PDXostc/rvi_v2x_hardware/Simulation/ACTIVE ANTENNA.asc

C1: cap; {ccap}; V=6.3 Irms=8.6m Rser=9.56706 Lser=0 mfg="KEMET" pn="C0402C331K9RAC" type="X7R"
C2: cap; 0.1µ; V=50 Irms=835m Rser=0.0936732 Lser=0 mfg="KEMET" pn="C1812C104K5RAC" type="X7R"
C3: cap; 150p
C4: cap; 100µ; V=35 Irms=.3 Rser=.26
C5: cap; 4.7µ; V=16 Irms=11 Rser=0.00897799 Lser=0 mfg="KEMET" pn="C1210C475K4RAC" type="X7R"
C6: cap; 100µ; V=35 Irms=.3 Rser=.26
C8: cap; 4.7µ; V=16 Irms=11 Rser=0.00897799 Lser=0 mfg="KEMET" pn="C1210C475K4RAC" type="X7R"
L1: ind; 56n; Ipk=0.45 Rser=0.4 Rpar=2563 Cpar=0.17p
L2: ind; 1p
L4: ind; 120n
R1: res; 50
R2: res; 50
R3: res; 50
V1: voltage; SINE(0 1 1200meg 0); AC 2 0; Rser=50
V2: voltage; 3.3; AC 0 0; Rser=.1
V3: voltage; SINE(0 1 1200meg 0); AC 2 0; Rser=50
Named nets: 0
.ac oct 100 1meg 10000meg
.step param ccap list 47p 56p 150p 270p 390p 470p
*.step param ind list 33n 47n 120n 220n
*.param ccap 530p
