PDXostc/rvi_v2x_hardware/Simulation/Charge Pump.asc

C1: cap; 100n
C2: cap; 1µ
D1: diode; 1N4148
D2: diode; 1N4148
D3: LED; AOT-2015
D4: LED; AOT-2015
D5: LED; AOT-2015
R1: res; 22
R2: res; 470
R3: res; 470
R4: res; 470
V1: voltage; PULSE(0 {volts} 0 {slew} {slew} {ton} {per} 0)
V2: voltage; {volts}
Named nets: 0
.tran .01
.param volts 2.7
.step param freq list 20k 100k
.param per {1/freq}
.param duty 0.5
.param ton  {per*duty}
.param slew 10n
