PDXostc/rvi_v2x_hardware/Simulation/J1850.asc

D1: diode; 1N4148
D2: diode; 1N4148
M1: nmos; BSZ340N08NS3
Q1: npn; 2N2222
Q2: npn; 2N2222
R1: res; 374
R2: res; 866
R3: res; 240
R4: res; 10k
R5: res; 2.2k
R6: res; 10k
R7: res; 10k
U1: LT1083
V1: voltage; 12
V2: voltage; 0
V3: voltage; 5
Named nets: 0
.tran 1m
