PDXostc/rvi_v2x_hardware/Simulation/RTCbu.asc

C1: cap; {CS}
I1: current; 10µ
Named nets: 0, VP
.IC V(VP) 3.2
.STEP PARAM CS LIST 1 0.5 .1 0.05
.tran 324000
